RedDuckBot/Mobile-Turret-Robot/bot_setup/stroam_libs/turret/include/turret/turret.hpp

#ifndef TURRET
#define TURRET

#include "digitalOutputDevice.hpp"
#include "servo.hpp"
#include <unistd.h>

//Define pulse width ranges for base servo and pusher rod servo
#define MAX_BASE_SERVO 2500
#define MIN_BASE_SERVO 550
#define MAX_PUSHER_SERVO 2200
#define MIN_PUSHER_SERVO 800 

namespace turret
{
    class Turret
    {
        public:
            Turret(
                //Pins defined as GPIO pins
                unsigned int laser_pin=26,
                unsigned int shooting_motors_pin=16,
                unsigned int base_serov_pin=13,
                unsigned int pusherRod_pin=12
            );
            void move_to_pos(int angle);
            void laser_on();
            void laser_off();
            void fire();
            void move_rod_forward();
            void move_rod_backward();

        private:
            outputDevice::DigitalOutputDevice laser_;
            outputDevice::DigitalOutputDevice shootingMotors_;
            stroams_servo::Servo baseServo_;
            stroams_servo::Servo pusherRodServo_;
    };
}
#endif
